zfeuers1/z-zener-zero/components/MAX-M10S-00B/MAX-M10S-00B.md

# MAX-M10S

## Standard precision GNSS module

### Professional grade

#### Integration manual



#### Abstract

This document describes the features and application of the u-blox MAX-M10S module. The MAX-M10S module provides an ultra-low-power standard precision GNSS receiver for high-performance asset-tracking applications.# Document information

|  Title | MAX-M10S  |
| --- | --- |
|  Subtitle | Standard precision GNSS module  |
|  Document type | Integration manual  |
|  Document number | UBX-20053088  |
|  Revision and date | R04  |
|  Disclosure restriction | C1-Public  |

This document applies to the following products:

|  Product name | Type number | FW version | IN/PCN reference | RN reference  |
| --- | --- | --- | --- | --- |
|  MAX-M10S | MAX-M10S-00B-01 | ROM SPG 5.10 | UBX-22012689 | UBX-22001426  |

u-blox or third parties may hold intellectual property rights in the products, names, logos and designs included in this document. Copying, reproduction, or modification of this document or any part thereof is only permitted with the express written permission of u-blox. Disclosure to third parties is permitted for clearly public documents only. The information contained herein is provided "as is" and u-blox assumes no liability for its use. No warranty, either express or implied, is given, including but not limited to, with respect to the accuracy, correctness, reliability and fitness for a particular purpose of the information. This document may be revised by u-blox at any time without notice. For the most recent documents, visit www.u-blox.com. Copyright © 2023, u-blox AG.# Contents 

1 System description ..... 6
1.1 Overview ..... 6
1.2 Architecture ..... 6
1.2.1 Block diagram ..... 6
1.3 Pin assignment ..... 7
2 Receiver configuration ..... 9
2.1 Basic receiver configuration ..... 9
2.1.1 Basic hardware configuration ..... 9
2.1.2 Internal LNA mode configuration ..... 9
2.1.3 GNSS signal configuration ..... 10
2.1.4 Communication interface configuration ..... 11
2.1.5 Message output configuration ..... 11
2.1.6 Antenna supervisor configuration ..... 12
2.1.7 High performance navigation update rate configuration ..... 13
2.2 Navigation configuration ..... 14
2.2.1 Dynamic platform ..... 14
2.2.2 Navigation input filters ..... 15
2.2.3 Navigation output filters ..... 16
2.2.4 Odometer filters ..... 16
2.2.5 Static hold ..... 17
2.2.6 Freezing the course over ground ..... 18
2.2.7 Super-Signal (Super-S) technology ..... 19
2.3 OTP memory configuration ..... 19
3 Receiver functionality ..... 20
3.1 Augmentation systems ..... 20
3.1.1 SBAS ..... 20
3.1.2 QZSS SLAS ..... 21
3.2 Communication interfaces and PIOs ..... 22
3.2.1 UART ..... 22
3.2.2 I2C ..... 23
3.2.3 PIOs ..... 26
3.3 Antenna ..... 28
3.3.1 Antenna supervisor ..... 28
3.4 Forcing receiver reset ..... 34
3.5 Security ..... 35
3.5.1 Configuration locking ..... 35
3.6 Power management ..... 35
3.6.1 Continuous mode ..... 35
3.6.2 Power save mode ..... 36
3.6.3 Backup modes ..... 42
3.7 Time ..... 42
3.7.1 Receiver local time ..... 43
3.7.2 GNSS time bases ..... 433.7.3 Navigation epochs ..... 44
3.7.4 iTow timestamps ..... 45
3.7.5 Time validity ..... 45
3.7.6 UTC representation ..... 46
3.7.7 Leap seconds ..... 46
3.7.8 Date ambiguity ..... 47
3.8 Time mark ..... 47
3.9 Time pulse ..... 48
3.9.1 Recommendations ..... 49
3.9.2 Time pulse configuration ..... 50
3.10 Time maintenance ..... 51
3.10.1 Real-time clock ..... 51
3.10.2 Time assistance ..... 51
3.10.3 Frequency assistance ..... 52
3.10.4 Clock drift assistance ..... 52
3.11 Protection level ..... 52
3.11.1 Introduction ..... 52
3.11.2 Interface ..... 53
3.11.3 Expected behavior ..... 54
3.12 Multiple GNSS assistance (MGA) ..... 54
3.12.1 Authorization ..... 55
3.12.2 Preserving MGA and operational data during power-off ..... 55
3.12.3 AssistNow offline ..... 55
3.12.4 AssistNow autonomous ..... 58
3.13 Data batching ..... 61
3.13.1 Introduction ..... 61
3.13.2 Setting up the data batching ..... 61
3.13.3 Retrieval ..... 62
3.14 CloudLocate ..... 62
3.14.1 CloudLocate measurements ..... 63
4 Hardware integration ..... 64
4.1 Power supply ..... 64
4.1.1 VCC ..... 64
4.1.2 V_IO ..... 64
4.1.3 V_BCKP ..... 64
4.1.4 Supply design examples ..... 65
4.2 RF interference ..... 66
4.2.1 In-band interference ..... 66
4.2.2 Out-of-band interference ..... 66
4.2.3 Spectrum analyzer ..... 67
4.3 RF front-end ..... 68
4.3.1 Internal LNA modes ..... 68
4.3.2 Out-of-band blocking immunity ..... 69
4.3.3 Out-of-band rejection ..... 70
4.3.4 Antenna power supply ..... 70
4.4 Layout ..... 71
4.4.1 Package footprint, copper and solder mask ..... 72
5 Product handling ..... 755.1 Safety ..... 75
5.1.1 ESD precautions ..... 75
5.1.2 Safety precautions ..... 75
5.2 Packaging ..... 76
5.2.1 Reels ..... 76
5.2.2 Tapes ..... 76
5.2.3 Moisture sensitivity level ..... 77
5.3 Soldering ..... 77
Appendix ..... 81
A Migration ..... 81
A. 1 Hardware changes ..... 81
A. 2 Software changes ..... 83
B Reference designs ..... 85
B. 1 Typical design ..... 85
B. 2 Antenna supervisor designs ..... 86
C External components ..... 89
C. 1 Standard capacitors ..... 89
C. 2 Standard resistors ..... 89
C. 3 Inductors ..... 89
C. 4 Operational amplifier ..... 90
C. 5 Open drain buffers ..... 90
C. 6 Antenna supervisor switch transistors ..... 90
Related documents ..... 91
Revision history ..... 92# 1 System description 

This section gives an overview of the MAX-M10S receiver, and outlines the basics of operation with the receiver.

### 1.1 Overview

MAX-M10S module features the u-blox M10 standard precision GNSS platform and provides exceptional sensitivity and acquisition time for all L1 GNSS signals.

The M10 platform supports concurrent reception of four GNSS (GPS, GLONASS, Galileo, and BeiDou). The high number of visible satellites enables the receiver to select the best signals. This maximizes the position availability, in particular under challenging conditions such as in deep urban canyons.
u-blox Super-S (Super-Signal) technology offers great RF sensitivity and can improve the dynamic position accuracy with small antennas or in non-line-of-sight scenarios.

The extremely low power consumption of 25 mW in continuous tracking mode allows great power autonomy for all battery-operated devices, such as asset trackers, without compromising on GNSS performance.

For maximum sensitivity in passive antenna designs, MAX-M10S integrates an LNA followed by a SAW filter in the RF path.

MAX-M10S offers backwards pin-to-pin compatibility with products from the previous u-blox generations, which saves the designer's effort and reduces costs when upgrading designs to the advanced low-power u-blox M10 GNSS technology.

### 1.2 Architecture

The MAX-M10S receiver provides all the necessary RF and baseband processing to enable multiconstellation operation. The block diagram below shows the key functionality.

### 1.2.1 Block diagram



Figure 1: MAX-M10S block diagram# 1.3 Pin assignment 



Figure 2: MAX-M10S pin assignment

| Pin no. | Name | PIO no. | I/O | Description | Remarks |
| :--: | :--: | :--: | :--: | :--: | :--: |
| 1 | GND | - | - | - | Connect to GND |
| 2 | TXD | 1 | 0 | UART TX | If not used, leave open. Alternative functions ${ }^{1}$. |
| 3 | RXD | 0 | I | UART RX | If not used, leave open. Alternative functions ${ }^{1}$. |
| 4 | TIMEPULSE | 4 | 0 | Time pulse signal | See section TIMEPULSE for more information. Alternative functions ${ }^{1}$. |
| 5 | EXTINT | 5 | I | External interrupt | See EXTINT for more information. Alternative functions ${ }^{1}$. |
| 6 | V_BCKP | - | I | Backup voltage supply. | Leave open if no external backup supply. See V_BCKP for more information. |
| 7 | V_IO | - | I | IO voltage supply | See V_IO for more information. |
| 8 | VCC | - | I | Main voltage supply | See VCC for more information. |
| 9 | RESET_N | - | I | System reset (active low) | It has to be low for at least 1 ms to trigger a reset. Leave open if not used. <br> See RESET_N section for more information. |
| 10 | GND | - | - | - | Connect to GND |
| 11 | RF_IN | - | I | GNSS signal input | The RF signal line is DC blocked internally. The line must match the $50 \Omega$ impedance. <br> See sections RF front-end and Layout for more information about the RF signal considerations. |
| 12 | GND | - | - | - | Connect to GND |
| 13 | LNA_EN | - | 0 | On/Off external LNA or active antenna | This pin cannot be used for another purpose as it also controls the internal LNA. <br> See LNA_EN for more information. |

[^0]
[^0]:    1 Alternatively, this pin can be used for ANT_DETECT, ANT_SHORT_N, TX_READY, and Data batching. Care must be taken when the assigned function sets the pin as an output.| Pin no. | Name | PIO no. | I/O | Description | Remarks |
| :--: | :--: | :--: | :--: | :--: | :--: |
| 14 | VCC_RF | - | 0 | Output voltage RF section | This pin supplies a filtered voltage that can be used for optional external active antenna or LNA. This pin is internally connected to VCC through a ferrite bead. |
| 15 | VIO_SEL | - | I | Voltage selector for V_IO supply | Connect to GND for 1.8 V supply, or leave open for 3.3 V supply |
| 16 | SDA | 2 | I/O | I2C data | If not used, leave open. Alternative functions ${ }^{1}$. |
| 17 | SCL | 3 | I | I2C clock | If not used, leave open. Alternative functions ${ }^{1}$. |
| 18 | SAFEBOOT_N | - | I | Safeboot mode | To enter safeboot mode, set this pin to low at receiver's startup. Otherwise, leave it open. <br> The SAFEBOOT_N pin is internally connected to TIMEPULSE pin through a $1 \mathrm{k} \Omega$ series resistor. |

Table 1: MAX-M10S pin assignment# 2 Receiver configuration 

The configuration determines all aspects of the GNSS receiver operation and therefore this section is essential reading for the successful integration of the MAX-M10S.

MAX-M10S is configured using UBX configuration interface keys. The configuration database in the receiver's RAM holds the current configuration, which is used by the receiver at runtime. It is constructed on startup of the receiver from several sources of configuration. For more information on receiver configuration, see the interface description [3].

A configuration setting stored in the RAM remains effective until power-down or reset. The RAM content is cleared by any of the following:

- Activating the RESET_N pin
- A UBX-CFG-RST message excluding GNSS stop (resetMode 0x08) and GNSS start (resetMode $0 \times 09)$
- Entering software standby mode
- Using external control in power save mode (PSM) to enter the inactive state
- Entering the off state of the PSM on/off operation (PSMOO)

It is therefore recommended to apply runtime configuration on both RAM and battery-backed RAM (BBR) layers.

The configuration stored in BBR is also cleared by a RESET_N signal or a UBX-CFG-RST message with reset mode set to a hardware reset (resetMode $0 \times 00$ and $0 \times 04$ ), but otherwise will be used as long as the backup battery supply remains.

CAUTION The configuration interface has changed from earlier u-blox positioning receivers. Users must adopt the configuration interface described in this document.

The configuration interface settings are stored in a database consisting of separate configuration items. An item is made up of a pair consisting of a key ID and a value. Related items are grouped together and identified under a common group name: CFG-GROUP-*; a convention used in u-center 2 and within this document. Within u-center 2, a configuration group is identified as "Group name" and the configuration item is identified as the "item name" in the "Device configuration" window.

The UBX messages available to change or poll the configurations are the UBX-CFG-VALSET, UBX-CFG-VALGET, and UBX-CFG-VALDEL messages. For more information about these messages and the configuration keys, see the configuration interface section in the interface description [3].

### 2.1 Basic receiver configuration

This section summarizes the basic receiver configuration most commonly used.

### 2.1.1 Basic hardware configuration

The MAX-M10S receiver is configured with the default settings during the module production. The receiver starts up and is fully operational as soon as proper power supply, communication interfaces and antenna signal from the host application device are connected.

### 2.1.2 Internal LNA mode configuration

u-blox 10 receivers support three modes for the internal low-noise amplifier (LNA): normal gain, low gain, and bypass mode. The MAX-M10S default is the low-gain mode. With a high-gain external active antenna, the bypass mode can be used. The normal-gain mode is not recommended for MAXM10S.The internal LNA mode can be configured at run time in BBR and RAM memory using the configuration item CFG-HW-RF_LNA_MODE and applying a software reset by sending UBX-CFGRST message. Refer to Forcing receiver reset for more information.

The internal LNA mode can also be permanently configured in the receiver's one-time programmable (OTP) memory. Changes to the bits in the OTP memory cannot be modified after they are programmed. The OTP configuration is only done once in production, and is subsequently applied automatically at every startup.

The default gain mode is pre-configured in the receiver and does not require configuration in production. The configuration string for setting the internal LNA mode in the OTP memory is given in Table 2.

OTP configuration is permanent and cannot be reverted. Configuration at run time in BBR and RAM memory is still possible.

| Internal LNA mode | Configuration string |
| :-- | :-- |
| Low gain | Default |
| Bypass | B5 62 06 41 10 00 03 00 05 1F 79 B2 0A E5 28 EF 12 05 9F FF FF FF 62 FB |

Table 2: Internal LNA mode configuration in OTP memory
To configure the internal LNA mode in OTP memory:

1. Power up the system.
2. Test the communication interface by polling the UBX-MON-VER message.
3. Send the configuration string in Table 2.
4. Power the receiver off and on or send UBX-CFG-RST message (the reset type must be set to a hardware reset). The new internal LNA setting is applied at startup.
5. Verify that the configuration item is correctly set by polling CFG-HW-RF_LNA_MODE at RAM layer using the UBX-CFG-VALGET message.
6. The OTP memory configuration is completed.

# 2.1.3 GNSS signal configuration 

MAX-M10S supports concurrent reception of four major GNSS constellations using the GPS L1C/A, Galileo E1, BeiDou B1C, and GLONASS L1OF signals. BeiDou B1I signal is also supported, but cannot be used simultaneously with BeiDou B1C or GLONASS L1OF signals. The default configuration is concurrent reception of GPS, Galileo and BeiDou B1I with QZSS and SBAS enabled.

BeiDou B1I signal cannot be used simultaneously with BeiDou B1C or GLONASS L1OF signals.
GNSS constellations and signals can be configured using the CFG-SIGNAL-* configuration group. Each GNSS constellation can be enabled or disabled independently except for QZSS and SBAS, which are functional only with GPS. In addition to the configuration key for each constellation, there is a configuration key for each signal supported by the firmware. Unsupported combinations are rejected with a UBX-ACK-NAK message, and the warning "inv sig cfg" is sent via UBX-INF and NMEATXT messages (if enabled).

For example, if CFG-SIGNAL-GPS_ENA is set to zero, all signals from the GPS constellation are disabled. Alternatively, if CFG-SIGNAL-GPS_L1CA_ENA is set to zero, only the GPS L1 C/A signal is disabled.

Any change to the signal configuration items triggers a restart of the GNSS subsystem. This takes a short time period, so the host application should wait for message acknowledgement and a margin of 0.5 seconds prior to sending any further commands.It is recommended to enable QZSS L1C/A when GPS L1C/A is enabled in order to mitigate possible cross-correlation issues between the signals.

Refer to the Interface description [3] for more information on the CFG-SIGNAL-* configuration group.

# 2.1.3.1 BeiDou B1I and B1C signals

BeiDou B1I and B1C signals differ in terms of the center frequency, bandwidth, and modulation. Therefore, there are differences in performance and supported GNSS signals and features.

## Benefits of using BeiDou B1I signal:

BeiDou B1I offers superior GNSS performance. High start-up sensitivity and fast time-to-first-fix (TTFF) enable acquisition of a large number of BeiDou satellites. The tracking and reacquisition sensitivity for acquired signals is approximately at the same level for BeiDou B1I and B1C.

- Faster TTFF and higher start-up sensitivity. BeiDou B1I signals are acquired significantly faster and at a lower signal level than BeiDou B1C signals.
- Better availability. Higher start-up sensitivity results in a larger number of BeiDou satellites tracked and used in navigation solution especially at low signal level.
- AssistNow Online support. Enhanced start-up sensitivity and TTFF.
- Power save mode (PSM) support. PSM cyclic tracking (PSMCT) and on/off (PSMOO) mode operation are supported.

## Benefits of using BeiDou B1C signal:

BeiDou B1C signal has the same center frequency as GPS L1 C/A enabling concurrent use of 4 GNSS constellations. Multi-GNSS configurations with BeiDou B1C also have a lower power consumption compared to those with BeiDou B1I.

- Concurrent reception of 4 GNSS with GPS L1 C/A, Galileo E1, BeiDou B1C, and GLONASS L1OF.
- Lower power consumption. No additional frequency band required for BeiDou B1C in multiGNSS constellations resulting in a lower power consumption during acquisition and tracking phases.

### 2.1.4 Communication interface configuration

Several configuration groups allow configuring the operation mode of the communication interfaces. These include parameters for the data framing, transfer rate and enabled input/output protocols. See Communication interfaces and PIOs section for details. The configuration groups available for each interface are:

|  Interface | Configuration groups  |
| --- | --- |
|  UART | CFG-UART1-*, CFG-UART1INPROT-*, CFG-UART1OUTPROT-*  |
|  I2C | CFG-I2C-*, CFG-I2CINPROT-*, CFG-I2COUTPROT-*, CFG-TXREADY-*  |

Table 3: Interface configuration The UART baudrate in MAX-M10S is configured to 9600 baud which is different to the firmware default. This ensures backwards compatibility with previous generations of u-blox MAX modules.

### 2.1.5 Message output configuration

The receiver supports two protocols for output messages: industry-standard NMEA and u-blox UBX. Any message type can be enabled or disabled individually and the output rate is configurable.The message output rate is related to the frequency of an event. For example, the output message UBX-NAV-PVT (position, velocity, and time solution) is related to the navigation event, which generates a navigation epoch. In this case, the rate for each navigation epoch is defined by the configuration keys CFG-RATE-MEAS and CFG-RATE-NAV. For example, a value of 1000 ms in CFG-RATE-MEAS indicates that a measurement is done every second. If CFG-RATE-NAV is set to one (1), the solution is calculated for every measurement. This means that a navigation epoch is calculated every 1000 ms . If the rate is set to two (2), only the second measurement is used and the navigation epoch is calculated every two seconds. The same result is obtained if CFG-RATE-MEAS is set to 2000 ms , and CFG-RATE-NAV is set to one (1). Every 2000 ms a measurement is done, and in every measurement, a navigation epoch is calculated. However, this second option demands fewer resources and is the correct procedure when the navigation rate is changed. Setting a navigation rate value higher than one (1) is only needed when it is required that the raw measurement data is output at a higher rate than the navigation data.

The output rate for each message is defined in the CFG-MSGOUT-* configuration group. If the output rate of the message is set to one (1) on the UART interface, CFG-MSGOUT-UBX_NAV_PVT_UART1 = 1, the message is output for every navigation epoch. If the rate is set to two (2), the message is output for every other navigation epoch. If the rate is zero (0), then corresponding message is not output. As seen in this example, the rates of the output messages are individually configurable per communication interface.

Some messages, such as UBX-MON-VER, are non-periodic and are only output as an answer to a poll request.

The UBX-INF-* and NMEA-Standard-TXT information messages are non-periodic output messages that do not have a message rate configuration. Instead they can be enabled for each communication interface via the CFG-INFMSG-* configuration group.

All message output is additionally subject to the protocol configuration of the communication interfaces. Messages of a given protocol are not output unless the protocol is enabled for output on the interface. See Communication interface configuration for details.

The output rate of the NMEA-GxGSV message on the UART interface is configured to 5 in MAXM10S, which is different to the firmware default in order to avoid overloading the communication interface and buffers.

# 2.1.6 Antenna supervisor configuration 

This section gives an overview of the antenna supervisor configuration keys. The implementation of the antenna supervisor and a detailed description can be found in Antenna supervisor.

The antenna supervisor is used to control an active antenna. The configuration of the antenna supervisor allows the following:

- Control voltage supply to the antenna, which allows the antenna supervisor to cut power to the antenna in the event of a short circuit or optimize power to the antenna in power save modes.
- Detect a short circuit in the antenna and automatically recover the antenna supply after the short circuit is no longer present.
- Detect an open circuit, which can be used to indicate if the antenna has been disconnected.

Using some antenna supervisor features may require disabling the UART or I2C interface and reconfiguring the PIOs as antenna supervisor pins.

Table 4 describes the configuration items.

| Configuration item | Description | Comments |
| :-- | :-- | :-- |
| CFG-HW-ANT_CFG_VOLTCTRL | Enable active antenna voltage control |  || Configuration item | Description | Comments |
| :--: | :--: | :--: |
| CFG-HW-ANT_CFG_SHORTDET | Enable short circuit detection |  |
| CFG-HW-ANT_CFG_SHORTDET_POL | Short antenna detection polarity | Set to 1 if the required logic polarity is active-low (default). |
| CFG-HW-ANT_CFG_OPENDET | Enable open circuit detection |  |
| CFG-HW-ANT_CFG_OPENDET_POL | Open antenna detection polarity | Set to 1 if the required logic polarity is active-low (default). |
| CFG-HW-ANT_CFG_PWRDOWN | Power down antenna supply if short circuit is detected | Requires CFG-HW- <br> ANT_CFG_VOLTCTRL and CFG-HW- <br> ANT_CFG_SHORTDET to be enabled. |
| CFG-HW-ANT_CFG_PWRDOWN_POL | Power down antenna logic polarity | Set to 1 if the required logic polarity is active-high (default). |
| CFG-HW-ANT_CFG_RECOVER | Enable auto-recovery in the event of a short circuit | To use this feature, enable short circuit detection and CFG-HW- <br> ANT_CFG_PWRDOWN. |
| CFG-HW-ANT_SUP_SWITCH_PIN | PIO number of the pin used for switching antenna supply | PIO5 is recommended if available. This pin can be used as an LNA_EN signal to control an external LNA, especially if software standby mode or power save mode on/off (PSMOO) operation is used. |
| CFG-HW-ANT_SUP_SHORT_PIN | PIO number of the pin used for detecting a short circuit in the antenna supply | UART or I2C pins can be used for the short detection, depending on which interface is used for communication. |
| CFG-HW-ANT_SUP_OPEN_PIN | PIO number of the pin used for detecting open/disconnected antenna | UART or I2C pins can be used for the short detection, depending on which interface is used for communication. |

Table 4: Antenna supervisor configuration
It is possible to obtain the status of the antenna supervisor from the UBX-MON-RF message. Refer to the interface manual for the description of the antStatus and antPower fields [3]. In addition, any changes in the status of the antenna supervisor are reported to the host interface as ANTSTATUS in NMEA notice messages.

| ANTSTATUS | Description |
| :-- | :-- |
| OFF | Antenna is off |
| ON | Antenna is on |
| DONTKNOW | Antenna power status is not known |

Table 5: Antenna power status

# 2.1.7 High performance navigation update rate configuration 

The navigation update rate is a GNSS configuration item which determines how many position fixes the receiver calculates and outputs per second. The maximum achievable navigation update rate depends on the number of GNSS signals the receiver is tracking. Depending on the geographical location and GNSS constellations enabled, the number of tracking channels in use may vary. In particular, in Asia there is a large number of BeiDou satellites available potentially limiting the maximum achievable navigation update rate. In regions with a lower number of available BeiDou satellites, a higher navigation rate is achieved.

The maximum navigation update rate given in the datasheet is provided for a minimum of $98 \%$ position fix rate, i.e., up to $2 \%$ position fixes can get lost in case of high availability of signals. The navigation update rate can be increased beyond the maximum value stated in the datasheet. However, this may result in a reduced fix rate if a very large number of satellites is tracked.u-blox M10 devices are optimized for low power consumption and come with the default CPU clock rate that supports the default navigation update rate stated in the product datasheet. However, it is possible to achieve a higher navigation update rate by configuring the device for a higher clock rate. This supports the high performance navigation update rate with minor increase in power consumption.

For the high navigation update rates, increase the communication speed and reduce the number of enabled messages.

The high performance navigation update rate can be configured in the device's one-time programmable (OTP) memory. The OTP configuration is only done once, and is subsequently applied automatically at every startup. The configuration string for setting the high CPU clock rate in the OTP memory is given in Table 6. This occupies 18 bytes of OTP memory space.

Changes made in the OTP configuration are permanent and cannot be reverted.

|  CPU clock | Configuration string  |
| --- | --- |
|  Default CPU clock | Default  |
|  High CPU clock | B5 62064110000300041 F 545 E 79 BF 28 EF 1205 FD FF FF FF 8F 0D B5 6206411 C 000401 A4 10 BD 34 F9 1228 EF 12050500 A4 4000 B0 710 B 0 A 00 A4 4000 D8 B8 05 DE AE  |

Table 6: High performance navigation update rate configuration in OTP memory To configure the high performance navigation update rate in OTP memory:

1. Power up the device.
2. Test the communication interface by polling the UBX-MON-VER message.
3. Send the configuration string provided in Table 6. The device returns two UBX-ACK-ACK messages with sequence of bytes B5 620501020006414 F 78.
4. Set the device reset to a hardware reset. Power the device off and on or send the UBX-CFG-RST message to the device. The higher clock setting is applied at startup.
5. To verify that the configuration item is correctly set,
6. send the following sequence to the receiver: B5 62068 B 1400000400000100 A4 4003 00 A4 400500 A4 400 A 00 A4 404 C 15
7. receive a UBX-CFG-VALGET message with the following sequence: B5 62068 B 24000104 00000100 A4 4000 B0 710 B 0300 A4 4000 B0 710 B 0500 A4 4000 B0 710 B 0 A 00 A4 4000 D8 B8 057681
8. receive a UBX-ACK-ACK message with the following sequence: B5 6205010200068 B 99 C2
9. The OTP memory configuration is completed and verified.

# 2.2 Navigation configuration

This section presents various configuration options related to the navigation engine. These options can be configured through CFG-NAVSPG-* configuration keys.

### 2.2.1 Dynamic platform

The dynamic platform model can be configured through the CFG-NAVSPG-DYNMODEL configuration item. For the supported dynamic platform models and their details, see Table 7 and Table 8.

|  Platform | Description  |
| --- | --- |
|  Portable | Applications with low acceleration, e.g. portable devices. Suitable for most situations.  ||  Platform | Description  |
| --- | --- |
|  Stationary | Used in timing applications (antenna must be stationary) or other stationary applications. Velocity restricted to $0 \mathrm{~m} / \mathrm{s}$. Zero dynamics assumed.  |
|  Pedestrian | Applications with low acceleration and speed, e.g. how a pedestrian would move. Low acceleration assumed.  |
|  Automotive | Used for applications with equivalent dynamics to those of a passenger car. Low vertical acceleration assumed.  |
|  At sea | Recommended for applications at sea, with zero vertical velocity. Zero vertical velocity assumed. Sea level assumed.  |
|  Airborne <1g | Used for applications with a higher dynamic range and greater vertical acceleration than a passenger car. No 2D position fixes supported.  |
|  Airborne <2g | Recommended for typical airborne environments. No 2D position fixes supported.  |
|  Airborne <4g | Only recommended for extremely dynamic environments. No 2D position fixes supported.  |
|  Wrist | Only recommended for wrist-worn applications. Receiver will filter out arm motion.  |

Table 7: Dynamic platform models

|  Platform | Max altitude [m] | Max horizontal velocity [m/s] | Max vertical velocity [m/s] | Sanity check type | Max position deviation  |
| --- | --- | --- | --- | --- | --- |
|  Portable | 12000 | 310 | 50 | Altitude and velocity | Medium  |
|  Stationary | 9000 | 10 | 6 | Altitude and velocity | Small  |
|  Pedestrian | 9000 | 30 | 20 | Altitude and velocity | Small  |
|  Automotive | 6000 | 100 | 15 | Altitude and velocity | Medium  |
|  At sea | 500 | 25 | 5 | Altitude and velocity | Medium  |
|  Airborne <1g | 80000 | 100 | 6400 | Altitude | Large  |
|  Airborne <2g | 80000 | 250 | 10000 | Altitude | Large  |
|  Airborne <4g | 80000 | 500 | 20000 | Altitude | Large  |
|  Wrist | 9000 | 30 | 20 | Altitude and velocity | Medium  |

Table 8: Dynamic platform model details Applying dynamic platform models designed for high acceleration systems (e.g. airborne <2g) can result in a higher standard deviation in the reported position.

If a sanity check against a limit of the dynamic platform model fails, then the position solution becomes invalid. Table 8 shows the types of sanity checks which are applied for a particular dynamic platform model.

# 2.2.2 Navigation input filters

The navigation input filters in the CFG-NAVSPG-* configuration group control how the navigation engine handles the input data that comes from the satellite signal.

|  Configuration item | Description  |
| --- | --- |
|  CFG-NAVSPG-FIXMODE | By default, the receiver calculates a 3D position fix if possible but reverts to 2D position if necessary (auto 2D/3D). The receiver can be forced to only calculate 2D (2D only) or 3D (3D only) positions.  |
|  CFG-NAVSPG-CONSTR_ALT, CFG-
NAVSPG-CONSTR_ALTVAR | The fixed altitude is used if fixMode is set to 2D only. A variance greater than zero must also be supplied.  |
|  CFG-NAVSPG-INFIL_MINELEV | Minimum elevation of a satellite above the horizon to be used in the navigation solution. Low-elevation satellites may provide degraded accuracy, due to the long signal path through the atmosphere.  |
|  CFG-NAVSPG-INFIL_MINSVS, CFG-
NAVSPG-INFIL_MAXSVS | Minimum and maximum number of satellites to use in the navigation solution. There is an absolute maximum limit of 32 satellites that can be used for navigation.  || Configuration item | Description |
| :-- | :-- |
| CFG-NAVSPG-INFIL_NCNOTHRS, | A navigation solution will only be attempted if there is at least the given number of |
| CFG-NAVSPG-INFIL_CNOTHRS | satellites with signals at least as strong as the given threshold. |

Table 9: Navigation input filter parameters
If the receiver has only three satellites for calculating a position, the navigation algorithm uses a constant altitude to compensate for the missing fourth satellite. This is called a 2D fix. The constant altitude value is taken from the last successful 3D fix using a minimum of four available satellites.
$\square$ u-blox receivers do not calculate any navigation solution with fewer than three satellites.

# 2.2.3 Navigation output filters 

The result of a navigation solution is initially classified by the fix type (as detailed in the fixType field of UBX-NAV-PVT message). This distinguishes between failures to obtain a fix at all ("No Fix") and cases where a fix has been achieved, which are further subdivided into specific types of fixes (for example, 2D, 3D ).

Where a fix has been achieved, the fix is checked to determine whether it is valid or not. A fix is only valid if it passes the navigation output filters as defined in CFG-NAVSPG-OUTFIL. In particular, both PDOP and accuracy values must be below the respective limits.

Important: Users are recommended to check the gnssFixOK flag in the UBX-NAV-PVT or the NMEA valid flag. Fixes not marked as valid should not be used.

UBX-NAV-STATUS message also reports whether a fix is valid in the gpsFixOK flag. These messages have only been retained for backwards compatibility and it is recommended to use the UBX-NAV-PVT message.

### 2.2.4 Odometer filters

### 2.2.4.1 Speed (3D) low-pass filter

The CFG-ODO-OUTLPVEL configuration item activates a speed (3D) low-pass filter. The output of the speed low-pass filter is available in the UBX-NAV-VELNED message (speed field). The filtering level can be set via the CFG-ODO-VELLPGAIN configuration item and must be between 0 (heavy lowpass filtering) and 255 (weak low-pass filtering).

The internal filter gain is computed as a function of speed. Therefore, the level as defined in the CFG-ODO-VELLPGAIN configuration item defines the nominal filtering level for speeds below 5 $\mathrm{m} / \mathrm{s}$.

### 2.2.4.2 Course over ground low-pass filter

The CFG-ODO-OUTLPCOG configuration item activates a course over ground low-pass filter when the speed is below $8 \mathrm{~m} / \mathrm{s}$. The output of the course over ground (also named heading of motion 2D) low-pass filter is available in the UBX-NAV-PVT message (headMot field), UBX-NAV-VELNED message (heading field), NMEA-RMC message (cog field), and NMEA-VTG message (cogt field). The filtering level can be set via the CFG-ODO-COGLPGAIN configuration item and must be between 0 (heavy low-pass filtering) and 255 (weak low-pass filtering).

The filtering level as defined in the CFG-ODO-COGLPGAIN configuration item defines the filter gain for speeds below $8 \mathrm{~m} / \mathrm{s}$. If the speed is $8 \mathrm{~m} / \mathrm{s}$ or higher, no course over ground low-pass filtering is performed.# 2.2.4.3 Low-speed course over ground filter 

The CFG-ODO-USE_COG configuration item activates this feature and the CFG-ODOCOGMAXSPEED, CFG-ODO-COGMAXPOSACC configuration items are used to configure a lowspeed course over ground filter (also named heading of motion 2D). This filter derives the course over ground from position at very low speed. The output of the low-speed course over ground filter is available in the UBX-NAV-PVT message (headMot field), UBX-NAV-VELNED message (heading field), NMEA-RMC message (cog field) and NMEA-VTG message (cogt field). If the low-speed course over ground filter is not configured, then the course over ground is computed as described in section Freezing the course over ground.

### 2.2.5 Static hold

Static hold mode allows the navigation algorithms to decrease the noise in the position output when the velocity is below a predefined "Static Hold Threshold" level. This reduces the position wander caused by environmental factors such as multi-path and improves position accuracy especially in stationary applications. By default, static hold mode is disabled.

The CFG-MOT-GNSSSPEED_THRS configuration item defines the static hold speed threshold. If the speed drops below the defined "Static Hold Threshold", static hold mode is activated. Once static hold mode is active, the position output is kept static and the velocity is set to zero until there is evidence of movement again. Such evidence can be velocity, acceleration, changes of the valid flag (for example, position accuracy estimate exceeding the position accuracy mask, see also section Navigation output filters ), position displacement, etc.

The CFG-MOT-GNSSDIST_THRS configuration item defines the static hold distance threshold. If the distance between the estimated position and the static hold position exceeds the defined threshold, static hold mode is suspended or deactivated until there is evidence of no movement.


Figure 3: Position output in static hold mode

Figure 4: Flowchart of static hold mode

# 2.2.6 Freezing the course over ground 

If the low-speed course over ground filter is deactivated or inactive (see section Low-speed course over ground filter), the receiver derives the course over ground from the GNSS velocity information. If the velocity cannot be calculated with sufficient accuracy (for example, with bad signals) or if the absolute speed value is very low (under $0.1 \mathrm{~m} / \mathrm{s}$ ) then the course over ground value becomes inaccurate too. In this case the course over ground value is frozen, that is, the previous value is kept and its accuracy degrades over time. These frozen values will not be output in the NMEA messages NMEA-RMC and NMEA-VTG unless the NMEA protocol is explicitly configured to do so (see NMEA protocol configuration in the applicable interface description [3]).

Figure 5: Flowchart of course over ground freezing

# 2.2.7 Super-Signal (Super-S) technology 

In normal operating conditions, low signal strength (that is, signal attenuation) indicates possible degradation due to multi-path. The receiver trusts such signals less in order to preserve the quality of the position solution in poor signal environments. This feature can result in degraded performance in situations where the signals are attenuated for another reason, for example due to antenna placement. In this case, the weak signal compensation feature can be used to restore normal performance. There are three possible modes:

- Disabled: no weak signal compensation is performed
- Automatic: the receiver automatically estimates and compensates for the weak signal
- Configured: the receiver compensates for the weak signal based on a configured value

These modes can be selected using CFG-NAVSPG-SIGATTCOMP. In the case of the "configured" mode, the user should input the maximum C/NO observed in a clear-sky environment, excluding any outliers or unusually high values. Choose the configured value carefully, as it can have a large impact on the receiver performance.

### 2.3 OTP memory configuration

MAX-M10S contains a one-time programmable (OTP) memory. This is a non-volatile memory for storing configuration settings and ROM patches permanently in the device. The stored data cannot be modified after it has been initially programmed. The device applies the settings and ROM patches on the device startup.

As the space in the OTP memory is limited, only essential system configuration settings should be stored. The total space used for device configuration and ROM patches in the OTP memory must not exceed 64 bytes. Other settings can be stored in the BBR or sent from the host to the device on each device startup.

Ensure that the final configuration stored and optional ROM patches do not require more than 64 bytes of OTP memory space.# 3 Receiver functionality

This section provides a description of the receiver's functionality.

### 3.1 Augmentation systems

### 3.1.1 SBAS

MAX-M10S is capable of receiving multiple SBAS signals concurrently, even from different SBAS systems (WAAS, EGNOS, etc.). SBAS signals are recommended to be used only for correction data. SBAS signals can also be used for navigation, however they have low weighting and therefore only a minor impact on the navigation solution.

For receiving correction data, MAX-M10S automatically chooses the best SBAS satellite as its primary source. It will select only one since the information received from other SBAS satellites is redundant and could be inconsistent. The selection strategy is determined by the proximity of the satellites, the services offered by the satellite, the configuration of the receiver (test mode allowed/ disallowed, integrity enabled/disabled) and the signal link quality to the satellite.

If corrections are available from the chosen SBAS satellite and used in the navigation calculation, the differential status will be indicated in several output messages such as UBX-NAV-PVT, UBX-NAVSTATUS, UBX-NAV-SAT, NMEA-GGA, NMEA-GLL, NMEA-RMC, and NMEA-GNS. The UBX-NAVSBAS message provides detailed information about which corrections are available and applied. Refer to the interface description [3] for a detailed description of the messages.

The most important SBAS feature for accuracy improvement is the ionosphere correction parameters. The measured data from regional Ranging and Integrity Monitoring Stations (RIMS) are combined to make a Total Electron Content (TEC) map. This map is transferred to the receiver via SBAS satellites to allow a correction of the ionosphere delays on each received signal.

|  Message type | Message content | Source  |
| --- | --- | --- |
|  $0(0 / 2)$ | Test mode | All  |
|  1 | PRN mask assignment | Primary  |
|  $2,3,4,5$ | Fast corrections | Primary  |
|  6 | Integrity | Primary  |
|  7 | Fast correction degradation | Primary  |
|  9 | Satellite navigation (ephemeris) | All  |
|  10 | Degradation | Primary  |
|  12 | Time offset | Primary  |
|  17 | Satellite almanac | All  |
|  18 | Ionosphere grid point assignment | Primary  |
|  24 | Mixed fast / long-term corrections | Primary  |
|  25 | Long-term corrections | Primary  |
|  26 | Ionosphere delays | Primary  |

Table 10: Supported SBAS messages Each satellite serves a specific region and its correction signal is only useful within that region. Planning is crucial to determine the best possible configuration, especially in areas where signals from different SBAS systems can be received:- Example 1 - SBAS receiver in North America: In eastern parts of North America, make sure that EGNOS satellites do not take preference over WAAS satellites. The satellite signals from the EGNOS system should be disallowed by using the PRN scan mask (configuration key CFG-SBAS-PRNSCANMASK).
- Example 2 - SBAS receiver in Europe: Some WAAS satellite signals can be received in western parts as well as GAGAN SBAS satellites in some parts of Europe, therefore it is recommended that the satellites from all but the EGNOS system should be disallowed using the PRN scan mask.

Although u-blox receivers try to select the best available SBAS correction data, it is recommended to configure them to exclude unwanted SBAS satellites.

To configure the SBAS functionality, use the CFG-SBAS-* configuration group.

| Parameter | Description |
| :-- | :-- |
| CFG-SIGNAL-SBAS_ENA | Enabled/disabled status of the SBAS subsystem |
| CFG-SBAS-USE_TESTMODE | Allow/disallow SBAS usage from satellites in test mode |
| CFG-SBAS-USE_RANGING | Use the SBAS satellites for navigation (ranging) |
| CFG-SBAS-USE_DIFFCORR | Combined enable/disable switch for fast, long-term, and ionosphere corrections |
| CFG-SBAS-USE_INTEGRITY | Apply integrity information data |
| CFG-SBAS-PRNSCANMASK | Allows selectively enabling/disabling SBAS satellites |

Table 11: SBAS configuration parameters
When SBAS integrity data is applied, the navigation engine stops using all signals for which no integrity data is available (including all non-GPS signals). It is not recommended to enable SBAS integrity on borders of SBAS service regions in order not to inadvertently restrict the number of available signals.

SBAS integrity information is required for at least five GPS satellites. If this condition is not met, SBAS integrity data will not be applied.

When the receiver switches from a solution using correction data to a standard position solution, the reference frame of the output position will switch from that of the correction data to that of the standard position solution. For an SBAS solution, this reference frame will be aligned within a few cm of WGS84 (and modern ITRF realizations).

# 3.1.2 QZSS SLAS 

QZSS SLAS (Sub-meter Level Augmentation Service) is an augmentation technology, which provides correction data for pseudoranges of GPS, QZSS, and other major GNSS satellites. The correction stream is transmitted on the L1S signal at the L1 frequency ( 1575.42 MHz ).

For more information on QZSS SLAS, visit qzss.go.jp/en/.
Multiple QZSS SLAS signals can be received simultaneously. When receiving QZSS SLAS correction data, MAX-M10S will autonomously select the best QZSS satellite. The selection strategy is determined by the quality of the QZSS L1S signals, the receiver configuration (test mode allowed or not), and the location of the receiver with respect to the QZSS SLAS coverage area. When outside of this coverage area, the receiver will likely fall back to using SBAS corrections.

If QZSS SLAS corrections are used in the navigation solution, the differential status will be indicated in several output messages such as UBX-NAV-PVT, UBX-NAV-STATUS, UBX-NAV-SAT, NMEA-GGA, NMEA-GLL, NMEA-RMC, and NMEA-GNS. The UBX-NAV-SLAS message provides detailed information about which corrections are available and applied. Refer to the interface description [3] for a detailed description of the messages.| Message type | Message content |
| :-- | :-- |
| 0 | Test mode |
| 47 | Monitoring station information |
| 48 | PRN mask |
| 49 | Data issue number |
| 50 | DGPS correction |
| 51 | Satellite health |

Table 12: Supported QZSS L1S SLAS messages for navigation enhancement
Use the configuration key CFG-SIGNAL-QZSS_L1S_ENA to enable QZSS L1S signal. For further QZSS SLAS functionality, use the CFG-QZSS-USE_SLAS* configuration keys.

| Parameter | Description |
| :-- | :-- |
| CFG-QZSS-USE_SLAS_DGNSS | Apply QZSS SLAS corrections |
| CFG-QZSS-USE_SLAS_TESTMODE | Allow the correction provided by QZSS satellites that are in test mode |
| CFG-QZSS- <br> USE_SLAS_RAIM_UNCORR | If this configuration is set, the receiver will try to estimate the position by using only <br> corrected measurements; if all corrected measurements are not available, it will not <br> use any corrections. If this configuration is not set, the receiver will mix corrected <br> and uncorrected measurements for the navigation solution. |

Table 13: QZSS SLAS configuration parameters
If the RAIM option is set, QZSS is the only GNSS time system that measurements can observe.

# 3.2 Communication interfaces and PIOs 

MAX-M10S supports communication over UART and I2C interfaces for communication with a host CPU. Each protocol can be enabled on several interfaces at the same time with individual settings for, for example, baud rate, message rates, and so on. In MAX-M10S, several protocols can be enabled on a single interface at the same time.

### 3.2.1 UART

MAX-M10S supports a Universal Asynchronous Receiver/Transmitter (UART) port consisting of an RX and a TX line. The UART can be used as a host interface which supports a configurable baud rate and protocol selection.

Neither handshaking signals nor hardware flow control signals are supported.
The UART baud rate can be configured for selected speeds. Different rates than these speeds are not supported for transmission and reception.

The UART RX interface will be disabled when more than 100 frame errors are detected during a one-second period. This can happen if the wrong baud rate is used or the UART RX pin is grounded. An error message appears when the UART RX interface is re-enabled at the end of the one-second period.

| Baud rate | Data bits | Parity | Stop bits |
| :-- | :-- | :-- | :-- |
| 4800 | 8 | none | 1 |
| 9600 | 8 | none | 1 |
| 19200 | 8 | none | 1 |
| 38400 | 8 | none | 1 |
| 57600 | 8 | none | 1 |
| 115200 | 8 | none | 1 || Baud rate | Data bits | Parity | Stop bits |
| :-- | :-- | :-- | :-- |
| 230400 | 8 | none | 1 |
| 460800 | 8 | none | 1 |
| 921600 | 8 | none | 1 |

Table 14: Possible UART interface configurations
Allow a short time delay of typically 100 ms between sending a baud rate change message and providing input data at the new rate. Otherwise some input characters may be ignored or the port could be disabled until the interface is able to process the new baud rate.

The default baud rate is 9600 baud. Using a lower baud rate may cause buffering problems.
If there is too much data for the interface's bandwidth, the output buffer will fill up. Once the buffer space is exceeded, new messages to be sent will be dropped. To prevent message loss, the baud rate and the number of enabled messages should be selected carefully.

# 3.2.2 I2C 

An I2C interface is available for communication with an external host CPU in I2C Fast-mode. Backwards compatibility with Standard-mode I2C bus operation is not supported. The interface can be operated only in slave mode with a maximum bit rate of $400 \mathrm{kbit} / \mathrm{s}$. The interface can make use of clock stretching by holding the SCL line LOW to pause a transaction. In this case, the bit transfer rate is reduced. The maximum clock stretching time is 20 ms .

The SCL and SDA pins have internal pull-up resistors which should be sufficient for most applications. However, depending on the clock speed of the host and the capacitive load on the I2C lines, additional external pull-up resistors may be necessary. The higher the speed and the capacitance load, the lower the pull-up resistor needs to be.

To poll or set the I2C address, use the CFG-I2C-ADDRESS configuration item (see the u-blox M10 interface description [3]). The CFG-I2C-ADDRESS configuration item is an 8-bit value containing the I2C address in the 7 most significant bits plus a 0 as the least significant bit. Thus, the default address becomes $0 \times 84(10000100)$.

In designs where the host uses the same I2C bus to communicate with more than one u-blox receiver, each receiver's I2C address must be configured with a different value.

### 3.2.2.1 I2C register layout

As shown in Figure 6, there are 256 registers. The data registers 0 to 252, at addresses $0 \times 00$ to $0 x F C$, contain reserved information and must not be used. Hence, only the last three registers are left for communication. The registers $0 x F D$ and $0 x F E$ contain the currently available number of bytes to be read, while the register $0 x F F$ buffers the message stream. The $0 x F F$ address delivers a $0 x F F$ byte value if there is no data awaiting for transmission, or all the bytes have been read.

Figure 6: I2C register layout

# 3.2.2.2 Read access types 

The host can choose one of the following two modes:

- Random read access: the master first reads the number of available bytes at the 0xFD and 0xFE before accessing the data at 0xFF.
- Current address read access: the master directly reads the data at the register 0xFF, without knowing first if there is any data waiting. If there is no data, the read result is a 0xFF byte value. This mode basically skips the first step of the "random read access", as it does not address to any particular register.

Figure 7 shows the format of the "random access" form of the request.
Following the start condition from the master, the 7-bit device address and the RW bit (which is a logic low for write access) are clocked onto the bus by the master transmitter. The receiver answers with an acknowledge (logic low) to indicate that it recognizes the address.

Next, the 8-bit address of the register to be read must be written to the bus (0xFD for u-blox receivers). Following the receiver's acknowledgment, the master again triggers a start condition and writes the device address, but this time the RW bit is a logic high to initiate the read access. Now, the master can read 1 to N bytes from the receiver. The receiver will first deliver the byte value at 0xFD, followed by the value at 0xFE. At this point the master knows the number of bytes waiting at the 0xFF register, and by acknowledging again, the data stream follows. The data transfer will stop once the master emits a not-acknowledge response or a stop condition is triggered after the last byte has been read.

Figure 7: I2C random read access
If "current address" is used, an address pointer in the receiver is used to determine which register to read. This address pointer will increment after each read operation unless it is already pointing at register $0 x F F$, the highest addressable register, in which case it remains unaltered.

The initial value of this address pointer at startup is $0 x F F$, so by default all current address read operations will repeatedly read register $0 x F F$ and receive the next byte of message data (or $0 x F F$ value if no message data is waiting).


Figure 8: I2C current address read access
Only after addressing the slave, the receiver starts the data stream. If the master does not read data from the receiver for a certain timeout, the receiver assumes that the communication is broken and stops the data stream, preventing an overflow of the output buffer. This timeout is 1.5 seconds by default. However, it can be extended by setting the CFG-I2C-EXTENDEDTIMEOUT configuration item to true (see the MAX-M10S interface description [3]). By disabling the timeout, the receiver will only interrupt the data stream when the buffer is full. The buffer can store up to 4 kB and the time for an overflow event depends on the number of messages enabled.

# 3.2.2.3 Write access 

The receiver does not provide any write access except for writing UBX and NMEA messages to the receiver, such as configuration or aiding data. Therefore, the register set mentioned in section I2C register layout is not writeable.Following the start condition from the master, the 7-bit device address and the RW bit (which is a logic low for write access) are clocked onto the bus by the master transmitter. The receiver answers with an acknowledge (logic low) response to indicate that it is responsible for the given address.

The master can write 2 to N bytes to the receiver, generating a stop condition after the last byte being written. To properly distinguish from the write access to set the address counter in random read accesses, the number of data bytes must be at least 2.


Figure 9: I2C write access

# 3.2.3 PIOs 

This section describes the PIOs supported by MAX-M10S. All PIO active voltage levels are related to the V_IO supply voltage. All the inputs have internal pull-up resistors in normal operation and can be left open if unused.
$\sim$ When assigning a different function to a PIO, ensure that the default function is disabled where applicable. For example, disable the I2C interface with the CFG-I2C-ENABLED configuration key if I2C pins are used for antenna supervisor functions.

### 3.2.3.1 RESET_N

MAX-M10S provides a RESET_N pin to reset the receiver. The RESET_N pin is input-only with an internal pull-up resistor to V_IO and should be left open for normal operation. Driving RESET_N low for at least 1 ms will trigger a reset of the receiver. The RESET_N complies with the V_IO level and can be actively driven high.
$\sim$ Use RESET_N only in critical situations to recover the receiver. RESET_N resets the receiver and clears the BBR content including receiver configuration, real-time clock (RTC), and GNSS orbit data, triggering a cold start.
$\sim$ No capacitor should be placed at RESET_N to GND, otherwise it could trigger a reset on every startup.

### 3.2.3.2 SAFEBOOT_N

The SAFEBOOT_N pin is for future service, updates and reconfiguration.
$\sim$ The SAFEBOOT_N pin is internally connected to the TIMEPULSE pin through a $1 \mathrm{k} \Omega$ series resistor.

### 3.2.3.3 TIMEPULSE

The MAX-M10S features one time pulse output at the TIMEPULSE pin. This can only be configured in PIO04. The details about this feature are explained in the section Time pulse.The TIMEPULSE and SAFEBOOT_N functions share the same internal IC function. If this pin is low at receiver startup, the receiver will enter safeboot mode. However, in normal operation the pin outputs the time pulse signal. Make sure there is no load on this pin that could pull it low at startup.

# 3.2.3.4 LNA_EN 

The system can turn an optional external LNA on and off using the LNA_EN signal to optimize the power consumption. The LNA is turned on when LNA_EN is "high".

The LNA_EN signal is also used internally in MAX-M10S to control the integrated LNA. The polarity cannot be changed.

The LNA_EN signal can also be used as a part of antenna supervisor circuit to control an external LNA or antenna power supply.

### 3.2.3.5 EXTINT

MAX-M10S supports external interrupts at the EXTINT pin. The EXTINT pin has a fixed input voltage threshold with respect to V_IO. It can be used for functions such as accurate external Frequency assistance, Time assistance and Time mark reporting.

The EXTINT pin enables External control for host-controlled on/off operation of the receiver, and as a wake-up source for power save mode on/off operation (PSMOO). If configured for host-controlled on/off operation, the internal pull-up is disabled. Make sure the EXTINT input is always driven within the defined voltage level by the host.

The EXTINT pin can also be configured for another functionality.
EXTINT functionality is only available at the EXTINT pin.

### 3.2.3.6 TX_READY

The receiver has an internal message buffer for storing bytes to be sent to the host application. TX-ready feature in TX_READY pin enables I2C to have an associated signal to indicate that the buffer has bytes to be transmitted. The host application can wait on the signal instead of polling the interface.

The TX-ready signal is enabled and assigned to a selected pin with CFG-TXREADY configuration items. The polarity of the signal (active-low or active-high) and the threshold for amount of bytes in the buffer must also be configured. When the number of bytes in the buffer reaches the threshold, the TX-ready signal becomes active. The signal stays active until all of the bytes in the buffer have been transferred. The receiver has additional small transmit buffer for each interface. Up to 16 bytes may still need to be transferred to the host after the TX-ready signal has become inactive.

The TX-ready signal can be assigned to any pin. Old function on the pin must be disabled before the assigment. Pin assignment can be verified with the UBX-MON-HW3 message.

The threshold value of the CFG-TXREADY-THRESHOLD is presented as 8-byte (64 bit) chunks. Divide the desired threshold value by 8. E.g., value of 128 sets the TX-ready signal activation threshold to 1024 bytes. The threshold should not be set above 2048 bytes (256 8-byte chunks). Otherwise, the TX-ready signal may not be activated in time, and some messages may get discarded.

### 3.2.3.6.1 Extended TX timeout

If the host does not communicate over I2C for more than 1.5 seconds, the receiver assumes that the host is no longer using this interface and no more packets are scheduled for this interface. This mechanism can be changed by enabling "extended TX timeouts" (configuration key CFG-I2C-EXTENDEDTIMEOUT). When enabled, the receiver delays idling the interface until the allocated and undelivered bytes for this interface reach 4 kB . This feature is especially useful when using the TXready feature with a message output rate of less than once per second, and fetching data only when available, determined by the TX_READY pin becoming active.

# 3.3 Antenna 

This section explains the antenna supervisor feature and the available implementation options.

### 3.3.1 Antenna supervisor

An active antenna supervisor provides the means to check the antenna for open and short circuits and to shut off the antenna supply if a short circuit is detected. Once enabled, the active antenna supervisor produces status messages that are reported in NMEA and/or UBX protocols. MAX-M10S supports two antenna supervisor variants: three-pin and two-pin implementations.

The three-pin antenna supervisor is able to detect short and open circuits and control the antenna supply. The two-pin antenna supervisor is a reduced version which is able to control the antenna supply and detect short circuits.

An overview of the two antenna supervisor variants is given in Table 15. It is recommended to make use of the full capabilities of the antenna supervisor (detect open and short circuits, and control the antenna supply).

The antenna supervisor can be configured through the CFG-HW-ANT_* configuration items. This includes enabling and disabling as well as changing the polarity of each signal. The current configuration of the active antenna supervisor can also be checked by polling the related CFGHW_ANT_* configuration items.

The active antenna status can be determined by polling the UBX-MON-RF message or checking the NMEA notice messages. If an antenna is connected, the initial state after power-up is "Active Antenna OK" in the UBX-MON-RF message.

| Features | Three-pin | Two-pin |
| :-- | :-- | :-- |
| Short detection | Yes | Yes |
| Open detection | Yes | No |
| External components | Discrete and IC | Discrete and IC |
| Number of PIOs needed | Three | Two |

Table 15: Antenna supervisor overview

### 3.3.1.1 Three-pin antenna supervisor

An active antenna supervisor circuit uses the ANT_DETECT, ANT_OFF_N, and ANT_SHORT_N signals. The ANT_OFF_N signal is already enabled and assigned to the LNA_EN pin in MAX-M10S. The ANT_DETECT and ANT_SHORT_N signals can be assigned to any unused PIOs, which may require disabling the previous function of the PIOs. For example, the open circuit detection uses the ANT_DETECT signal, "high" = Antenna detected (antenna consumes current); "low" = Antenna not detected (no current drawn). To enable the three-pin antenna supervisor, the ANT_DETECT and ANT_SHORT_N signals must be enabled in the receiver configuration. The polarity of the ANT_DETECT and ANT_SHORT_N signals must also be defined in the receiver configuration based on the design use case.

The antenna can be supplied by VCC_RF or an external supply. Note that the supply voltage must be clean, as any noise could directly couple into the RF part of the GNSS receiver which affecting the overall GNSS performance.Refer to Reference designs for antenna supervisor examples and the required configuration.
Figure 10 presents the required three-pin antenna supervisor circuit and subsequent sections describe how to enable and monitor each feature.


Figure 10: MAX-M10S three-pin antenna supervisor
Table 16 presents a list of the external components required for implementing the three-pin antenna supervisor design in Figure 10. Refer to External components for the recommended parts and specification.

| Part | Description |
| :-- | :-- |
| C14 | Filtering capacitor |
| L3 | DC infeed inductor |
| T1, T2 | p-channel, n-channel MOSFET acting as a switch to control the antenna supply |
| U6 | Comparator (op-amp) |
| U7, U8 | Open drain buffers to shift voltage levels |
| R7 | Passive pull-up to control T1 |
| R8 | Current limiter in the event of a short circuit |
| R5 | Defines the threshold of the comparator |
| R6 | Defines the threshold of the comparator |

Table 16: Components in antenna supervisorThe threshold voltage (V_REF) of the comparator is defined by R5 and R6. It can be calculated as: $V_{-} R E F=R 6 /(R 6+R 5)^{*} V_{-} A N T$.

The open drain buffers shown in Figure 10 are not needed if V_ANT is the same voltage level as V_IO.

# 3.3.1.2 Two-pin antenna supervisor 

The reduced functionality antenna supervisor circuit is connected to two signals: antenna control (ANT_OFF_N) and antenna status detection (ANT_SHORT_N). The ANT_OFF_N signal is already enabled and assigned to the LNA_EN pin in MAX-M10S and the ANT_SHORT_N signal can be assigned to any unused PIO, which may require disabling the previous function of the PIO. To enable the reduced antenna supervisor, the ANT_SHORT_N signal must be enabled in the receiver configuration. The polarity of the ANT_SHORT_N signal must also be defined in the receiver configuration based on the design use case.

The antenna can be supplied by VCC_RF or an external supply. Note that the supply voltage must be clean, as any noise could directly couple into the RF part of the GNSS receiver affecting the overall GNSS performance.

Refer to Reference designs for antenna supervisor examples and the required configuration.
Figure 11 presents the required two-pin antenna supervisor circuit and subsequent sections describe how to enable and monitor each feature.


Figure 11: MAX-M10S two-pin antenna supervisor
Table 17 presents a list of the external components required for implementing the two-pin antenna supervisor design in Figure 11. Refer to External components for the recommended parts and specification.

| Part | Description |
| :-- | :-- |
| C14 | Filtering capacitor || Part | Description |
| :-- | :-- |
| T1, T2 | p-channel, n-channel MOSFET acting as a switch to control the antenna supply |
| U7 | Open drain buffers to shift voltage levels |
| R7 | Passive pull-up to control T1 |
| R8 | Current limiter in the event of a short circuit |

Table 17: Components in two-pin antenna supervisor
The open drain buffer shown in Figure 11 is not needed if V_ANT is the same voltage level as V_IO.

# 3.3.1.3 Antenna voltage control - ANT_OFF_N 

The antenna voltage control is enabled by default in MAX-M10S with the configuration item CFGHW-ANT_CFG_VOLTCTRL set to true (1).

The antenna status (as reported in UBX-MON-RF and UBX-INF-NOTICE messages) is not reported unless the antenna voltage control has been enabled.

Result:

- UBX-MON-RF: Antenna status = OK. Antenna power status = ON.
- ANT_OFF_N = active low. The pin is pulled high to enable an external antenna or LNA.

Startup message at power-up if the configuration is stored:
\$GNTXT, 01, 01, 02,ANTSUPERV=AC *00
\$GNTXT, 01, 01, 02, ANTSTATUS=INIT*3B
\$GNTXT, 01, 01, 02, ANTSTATUS=OK*25
ANTSUPERV=AC indicates that antenna control is activated.

### 3.3.1.4 Antenna short detection - ANT_SHORT_N

Enable the antenna short detection by setting the configuration item CFG-HW-ANT_CFG_SHORTDET to true (1).

Result:

- UBX-MON-RF: Antenna status = OK. Antenna power status = ON.
- ANT_OFF_N = active low to disable an external antenna. Therefore, the pin is pulled high to enable an external antenna.
- ANT_SHORT_N = active low to report a short circuit. The pin is default high (PIO pull-up enabled).

Startup message at power-up if the configuration is stored:
\$GNTXT, 01, 01, 02,ANTSUPERV=AC SD *37
\$GNTXT, 01, 01, 02, ANTSTATUS=INIT*3B
\$GNTXT, 01, 01, 02, ANTSTATUS=OK*25
ANTSUPERV=AC SD indicates that antenna control and short detection are activated.
If a short circuit is detected in the antenna (ANT_SHORT_N pulled low):
\$GNTXT, 01, 01, 02, ANTSTATUS=SHORT*73

- UBX-MON-RF: Antenna status = SHORT. Antenna power status = ON (automatic power-down is not enabled, CFG-HW-ANT_CFG_PWRDOWN is off by default).- ANT_OFF_N = high (external antenna enabled).

If CFG-HW-ANT_CFG_PWRDOWN has been enabled previously (set to true), the polarity of the ANT_OFF_N signal changes to power down (disable) the antenna supply when a short is detected.

After a detected antenna short, the reported antenna status continues to be reported as a SHORT. If auto-recovery is enabled for the antenna short detection, the antenna status can recover after a timeout of 60 seconds. Recovering the antenna status immediately requires either a power cycle or switching the antenna short detection off and on again.

# 3.3.1.5 Antenna short detection auto-recovery 

Enable the antenna short detection auto-recovery by setting the configuration item CFG-HWANT_CFG_RECOVER to true (1).

To use the auto-recovery feature, enable CFG-HW-ANT_CFG_PWRDOWN which requires CFG-HW-ANT_CFG_SHORTDET and CFG-HW-ANT_CFG_VOLTCTRL to be enabled.

Result:

- UBX-MON-RF: Antenna status = OK. Antenna power status = ON.
- ANT_OFF_N = active low. The pin is pulled high to enable an external antenna.
- ANT_SHORT_N = active low. The pin is default high (PIO pull-up enabled, to be pulled low if a SHORT is detected).

Startup message at power-up if the configuration is stored:
\$GNTXT, 01, 01, 02,ANTSUPERV=AC SD PDoS SR*3E
\$GNTXT, 01, 01, 02, ANTSTATUS=INIT*3B
\$GNTXT, 01, 01, 02, ANTSTATUS=OK*25
ANTSUPERV=AC SD PDoS SR (indicates short circuit recovery added - SR)
If short circuit is detected (ANT_SHORT_N pulled low):
\$GNTXT, 01, 01, 02, ANTSTATUS=SHORT*73

- UBX-MON-RF: Antenna status = SHORT. Antenna power status = OFF (automatic power-down is enabled).
- ANT_OFF_N = low (external antenna disabled).

After a timeout period of 60 seconds, the receiver retests the short circuit condition by enabling the antenna (i.e. pulling ANT_OFF_N high).

If a short is not present, the receiver reports antenna condition is OK:
\$GNTXT, 01, 01, 02, ANTSTATUS=OK*25
UBX-MON-RF: Antenna status = OK. Antenna power status = ON.

### 3.3.1.6 Antenna open circuit detection - ANT_DETECT

Enable the antenna open circuit detection by setting the configuration item CFG-HWANT_CFG_OPENDET to true (1).

Result:

- UBX-MON-RF: Antenna status = OK. Antenna power status = ON.
- ANT_OFF_N = active low. The pin is pulled high to enable an external antenna.- ANT_SHORT_N = active low. The pin is default high (PIO pull-up enabled, to be pulled low if a SHORT is detected).
- ANT_DETECT = active high. The pin is default high (PIO pull-up enabled, to be pulled low if the antenna is not detected).

Startup message at power-up if the configuration is stored:

```
$GNTXT,01,01,02,ANTSUPERV=AC SD OD PDoS SR*15
$GNTXT,01,01,02,ANTSTATUS=INIT*3B
$GNTXT,01,01,02,ANTSTATUS=OK*25
ANTSUPERV=AC SD OD PDoS SR (indicates open circuit detection added - OD)
```

If ANT_DETECT is pulled low to indicate no antenna connected:

```
$GNTXT,01,01,02,ANTSTATUS=OPEN*35
```

If ANT_DETECT is left floating or pulled high to indicate antenna connected:

```
$GNTXT,01,01,02,ANTSTATUS=OK*25
```

# 3.3.1.7 Antenna status reporting 

The antenna detection and antenna power status that is available in UBX-MON-RF and NMEA notice messages, is based on the antenna's physical state. The required antenna supervisor configuration keys depend on the selected antenna supervisor implementation (three-pin or two-pin).

Table 18 and Table 19 present a summary of the antenna status that is available in the antStatus and antPower fields of the UBX-MON-RF message. Refer to the interface description [3] for more information.

| Status | Description |
| :-- | :-- |
| DON'T KNOW | Antenna status is unknown. |
| INIT | Antenna power control feature is initialized (if CFG-HW-ANT_VOLTCTRL is enabled). |
| SHORT | A short is detected from the antenna input. That is, a lot of current is drawn from the active antenna. |
| OPEN | Antenna is not detected. That is, little or no current is drawn from the active antenna. |
| OK | Antenna is detected and no short is detected. |

Table 18: Available antenna detection status

| Status | Description |
| :-- | :-- |
| DON'T KNOW | CFG-HW-ANT_VOLTCTRL not configured. |
| OFF | GNSS OFF or a short is detected and CFG-HW-ANT_PWRDOWN is enabled. Note that this status <br> also applies when GNSS is restarted via CFG-RST or implicitly via CFG-GNSS, when GNSS selection is <br> reconfigured, or when GNSS is stopped in software standby mode and the off state of the power save <br> mode on/off (PSMOO). |
| ON | GNSS ON and no short/open is detected from the antenna input. Similarly, when there is a short and <br> CFG-HW-ANT_PWRDOWN is not enabled or auto-recovery is enabled. |

Table 19: Available antenna power status
Table 20 shows some possible combinations of the antenna supervisor configuration and the expected antenna status based on the physical state of the antenna. Note that the short detection takes priority over the open detection and " $X$ " in Table 20 implies an unconfigured or undetected physical state. In addition, CFG-HW-ANT_PWRDOWN requires that CFG-HW-ANT_CFG_VOLTCTRL and CFG-HW-ANT_CFG_SHORTDET are enabled. Likewise, CFG-HW-ANT_RECOVER requires CFG-HW-ANT_PWRDOWN to be enabled.The antenna supervisor is re-initialized after issuing a reset with RESET_N pin or changing any of the antenna supervisor configuration keys. Therefore, if the default configuration has changed, it is recommended to save the antenna supervisor configuration to BBR to ensure that the updated configuration is applied after a reset.

|  Configuration keys |  |  |  |  | Physical antenna state |  | Reported antenna status | |
| --- | --- | --- | --- | --- | --- | --- | --- | --- |
|  VOLTCTRL | SHORTDET | OPENDE | PWRDOWN | RECOVER | Short circuit Open circuit |  | antPower | antStatus  |
|  TRUE | $X$ | $X$ | $X$ | $X$ | NO | NO | ON | OK  |
|  TRUE | FALSE | $X$ | $X$ | $X$ | $X$ | NO |  | |
|  TRUE | $X$ | FALSE | $X$ | $X$ | NO | $X$ |  | |
|  TRUE | FALSE | FALSE | $X$ | $X$ | $X$ | $X$ |  | |
|  TRUE | FALSE | TRUE | $X$ | $X$ | $X$ | YES | ON | OPEN  |
|  TRUE | $X$ | TRUE | $X$ | $X$ | NO | YES |  | |
|  TRUE | TRUE | $X$ | FALSE | $X$ | YES | $X$ | ON | SHORT  |
|  TRUE | TRUE | $X$ | TRUE | $X$ | YES | $X$ | OFF | SHORT  |
|  FALSE | TRUE | $X$ | $X$ | $X$ | YES | $X$ | UNKNOWN | SHORT  |
|  FALSE | FALSE | TRUE | $X$ | $X$ | $X$ | YES | UNKNOWN | OPEN  |
|  FALSE | $X$ | TRUE | $X$ | $X$ | NO | YES | UNKNOWN | OPEN  |

Table 20: Antenna supervisor configuration and antenna states

# 3.4 Forcing receiver reset

GNSS receivers typically make a distinction between cold, warm, and hot start based on the type of valid information the receiver has during the restart.

- Cold start: in the cold start mode, the receiver has no information from the last position (e.g. time, velocity, frequency etc.) at startup. Therefore, the receiver must search the full time and frequency space, and all possible satellite numbers. If a satellite signal is found, it is tracked to decode the ephemeris (18-36 seconds under strong signal conditions), while the other channels continue to search satellites. Once there is a sufficient number of satellites with valid ephemeris, the receiver can calculate position and velocity data. Other GNSS receiver manufacturers call this the Factory startup mode.
- Warm start: in the warm start mode, the receiver has approximate information for time, position, and coarse satellite position data (Almanac). In this mode, the receiver normally needs to download ephemeris after power-up before it can calculate position and velocity data. As the ephemeris data is usually outdated after 4 hours, the receiver typically starts with a warm start if it has been powered down for more than 4 hours. In this scenario, several augmentations are possible. See Multiple GNSS assistance.
- Hot start: in the hot start mode, the receiver has been powered down only for a short time (4 hours or less), so that its ephemeris is still valid. Since the receiver does not need to download ephemeris again, this is the fastest startup method.

Using the UBX-CFG-RST message, you can force the receiver to reset and clear data, in order to see the effects of maintaining/losing such data between restarts. For this purpose, use the navBbrMask field in the UBX-CFG-RST message to initiate hot, warm, and cold starts, or a combination of startup modes.

The reset type can also be specified. This is not related to GNSS, but to the way the software restarts the system.

- Hardware reset uses the on-chip watchdog to electrically reset the chip. This is an immediate asynchronous reset. No stop events are generated.- Controlled software reset terminates all running processes in an orderly manner. Once the system is idle, restarts the receiver operation, reloads its configuration and starts to acquire and track GNSS satellites.
- Controlled software reset (GNSS only) only restarts the GNSS tasks, without reinitializing the full system or reloading any stored configuration.
- Hardware reset (after shutdown) uses the on-chip watchdog to reset the receiver after shutdown.
- Controlled GNSS stop stops all GNSS tasks. The receiver is not restarted, but stops any GNSSrelated processing.
- Controlled GNSS start starts all GNSS tasks.

Table 21 below contains an overview of the different reset types and the data that is cleared.

|  Reset type | Clears RAM | Clears BBR  |
| --- | --- | --- |
|  0x00 - Hardware reset (immediately), | Yes | Yes  |
|  0x04 - Hardware reset (after shutdown) |  | |
|  0x01 - Controlled Software reset | Yes | No  |
|  0x02 - Controlled Software reset (GNSS only), | No | No  |
|  0x08 - Controlled GNSS stop, |  | |
|  0x09 - Controlled GNSS start |  | |
|  RESET_N pin | Yes | Yes  |

Table 21: Overview of the available reset types

# 3.5 Security

The security concept of MAX-M10S covers:

- the integrity of the receiver
- communication between the receiver and the GNSS satellites

Some security functions monitor and detect threats and report them to the host system. Other functions mitigate threats and allow the receiver to operate normally.

### 3.5.1 Configuration locking

The receiver configuration can be locked so that further changes are no longer possible. The configuration can be locked by setting the configuration item CFG-SEC-CFG_LOCK to "true". This item can be set in the same way as all other configuration items on various layers.

If the configuration lock is set in BBR, it remains locked until the BBR is cleared. To test the function, set it in the RAM configuration layer. After the receiver's power cycle, the information in this layer is lost and the configuration lock is not set anymore.

### 3.6 Power management

u-blox receivers support different operating modes. These modes represent strategies of controlling the acquisition and tracking engines to achieve either the best possible performance or good performance with reduced power consumption.

### 3.6.1 Continuous mode

MAX-M10S uses dedicated signal processing engines optimized for signal acquisition and tracking. The acquisition engine actively searches for and acquires signals during cold starts or when insufficient signals are available during navigation. The tracking engine continuously tracks anddownloads all the almanac data and acquires new signals as they become available during navigation. The tracking engine consumes less power than the acquisition engine.

The current consumption is lower when a valid position is obtained quickly after the start of the receiver navigation, the entire almanac has been downloaded, and the ephemeris for each satellite in view is valid. If these conditions are not met, the search for the available satellites takes more time and consumes more power.

# 3.6.2 Power save mode 

Power save mode (PSM) allows a reduction in system power consumption by selectively switching parts of the receiver on and off. It is enabled with CFG-PM-OPERATEMODE and configured with items in the CFG-PM group.

Power save mode (PSM) has two modes of operation:

- Power save mode cyclic tracking (PSMCT) operation is used when position fixes are required in short periods of 0.5 s to 10 s .
- Power save mode on/off (PSMOO) operation is used for periods longer than 10 s , and can be in the order of minutes, hours, or days.

The mode of operation can be configured, and depending on the setting, the receiver demonstrates different behavior. In on/off operation the receiver switches between phases of startup/navigation and phases with low or almost no system activity (backup/sleep). In cyclic tracking the receiver does not shut down completely between fixes, but uses low-power tracking instead.

In PSMOO mode, the RAM memory is cleared during the off periods. Consequently, store the configuration in the BBR memory to maintain the settings.

GPS, GLONASS, BeiDou B1I, Galileo and QZSS signals are supported in power save mode. BeiDou B1C signal is not supported. The receiver is unable to download or process any SBAS data in power save mode and it is therefore recommended to disable SBAS.

BeiDou B1C is not supported in power save mode.

### 3.6.2.1 Operation

PSM is based on a state machine with five different states: Inactive for update, Inactive for search, Acquisition, Tracking and Power optimized tracking (POT) state.

- Inactive states: most parts of the receiver are switched off.
- Acquisition state: the receiver actively searches for and acquires signals. Maximum power consumption.
- Tracking state: the receiver continuously tracks and downloads data. Less power consumption than in the acquisition state.
- POT state: the receiver repeatedly loops through a sequence of tracking (Track), calculating the position fix (Fix), and entering an idle period (Idle). No new signal is acquired and no data is downloaded. The power consumption is much lower than in the tracking state.

The PSM state machine is described in Figure 12.

Figure 12: State machine

# 3.6.2.2 Acquisition timeout 

The receiver has internal, external, and user-configurable mechanisms that determine the time to be spent in acquisition state. This logic is put in place to ensure good performance and low power consumption in different environments and scenarios. This collective logic is referred to as acquisition timeout.

The configuration items related to acquisition timeout are described in section Configuration.
Internal mechanisms:

- If the receiver is able to acquire weak signals but not of the quality needed to get a fix, it will transition to the "Inactive for search" state after the timeout configured in MAXACQTIME or earlier if too few signals are acquired.
- If the receiver is unable to acquire any signals or it acquires a small number of extremely bad signals (e.g., no sky view), it will transition to the "Inactive for search" state after the timeout configured in MAXACQTIME.

User-configurable mechanisms:

- MINACQTIME is the minimum time that the receiver will spend in the "Acquisition" state. MINACQTIME is applicable only when no or very poor GNSS signal is available.
- MAXACQTIME is the maximum time that the receiver will spend in the "Acquisition" state.
- DONOTENTEROFF forces the receiver to stay awake and in the "Acquisition" state even when a fix is not possible.

External mechanisms:

- The receiver is forced to stay awake if EXTINTWAKE is enabled and the EXTINT pin is set to "high". The receiver is forced to stay in the "Inactive for search/Fix" states if EXTINTBACKUP is enabled and the EXTINT pin is set to "low".
- The receiver is forced to stay awake if EXTINTINACTIVE is enabled and the EXTINT pin is toggled. If EXTINT pin state is not changed for a longer time than EXTINTINACTIVITY, the receiver enters the "Inactive for search/Fix" states.# 3.6.2.3 Cyclic tracking 

Power save mode cyclic tracking (PSMCT) operation is described in Figure 13.
PSMCT supports 1 Hz and 2 Hz navigation update rates. In addition, longer update periods from 2 s to 10 s are supported at 1 s steps.


Figure 13: Cyclic tracking operation

- When the receiver is switched on, it first enters the "Acquisition" state. A larger number of signals tracked later helps the receiver to remain in the "POT" state if some signals get blocked and are lost. This may reduce the overall power consumption.
- If the receiver is able to acquire a valid position fix (one passing the navigation output filters) within the time given by the Acquisition timeout, it switches to the "Tracking" state and the ONTIME starts. Otherwise it enters the "Inactive for search" state and restarts after the configured search period (minus a start-up margin).
- Once the ONTIME is over, the "POT" state is entered. Setting the ONTIME to zero causes the receiver to enter the "POT" state as soon as possible.
- In the "POT" state the receiver continues to output position fixes according to the CFG-RATE-*.
- If the signal becomes weak or is lost during the "POT" state, the "Tracking" state is entered.
- Once the signal is good again and the newly started ONTIME is over, the receiver will re-enter the "POT" state.
- If the receiver cannot get a position fix in the "Tracking" state, it enters the "Acquisition" state. Should the acquisition fail as well, the "Inactive for search" state is entered. If DONOTENTEROFF is enabled and no fix is possible, the receiver will remain in the "Acquisition" state until a fix is possible and it will never enter the "Inactive for search" state.

### 3.6.2.4 On/Off mode

Power save mode on-off (PSMOO) operation is described in Figure 14.
PSMOO requires an RTC to maintain time.


Figure 14: On/off mode operation

- When the receiver is switched on, it first enters the "Acquisition" state.
- If it is able to acquire a valid position fix (one passing the navigation output filters) within the time given by the Acquisition timeout, it switches to the "Tracking" state and the ONTIMEstarts. Otherwise it enters the "Inactive for search" state and restarts after the configured search period (minus a startup margin).

- Once the ONTIME is over, the "Inactive for update" state is entered and the receiver restarts according to the configured update grid defined by GRIDOFFSET.
- If the signal is lost while in the "Tracking" state, the "Acquisition" state is entered. If the signal is not found within the acquisition timeout, the receiver enters the "Inactive for search" state. Otherwise the receiver will re-enter the "Tracking" state and stay there until the newly started ONTIME is over.

Entering the off state of the PSMOO operation clears the RAM memory including the receiver configuration. To maintain the configuration in PSMOO operation, store it on both RAM and battery-backed RAM (BBR) layers. Configuration in an optional flash memory is always maintained.

# 3.6.2.5 External control 

The operation of power save mode can be controlled externally using the EXTINT pin. This external control allows the user to decide when to wake up the receiver to obtain a fix and when to force the receiver into backup mode to save power. Operating the receiver externally through the EXTINT pin will override internal functions that coincide with that specific operation.

Enabling EXTINTWAKE prevents the receiver from entering Inactive states for as long as the EXTINT pin is held "high". In PSMOO, the receiver will therefore always be in the "Acquisition" or the "Tracking" state. In PSMCT, the receiver can in addition be in the "POT" state. When EXTINT is set "low" the receiver will continue with its configured behavior.

Enabling EXTINTBACKUP forces the receiver to enter Inactive states for as long as the EXTINT pin is held "low" until the next wakeup event. Any wakeup event can wake up the receiver even if the EXTINT pin is held "low". In this case, the receiver only wakes up to read the configuration pins and then re-enters the Inactive state.

If both EXTINTWAKE and EXTINTBACKUP are enabled at the same time, the receiver PSM operation is completely under external control. Setting EXTINT "high" wakes up the receiver to get a position fix and setting "low" puts the receiver into backup mode.

EXTINT pin control can also be used in continuous mode.
In PSMOO, an external wakeup source can be set. Any wake-up event will restart the receiver to try to obtain a position fix. Wakeup signals have no effect if the receiver is already in the "Acquisition", "Tracking", or "POT" state.

Setting the update period POSUPDATEPERIOD to zero causes the receiver to wait in the "Inactive for update" state until the host wakes it up. Setting the search period ACQPERIOD to zero causes the receiver to wait in the "Inactive for search" state indefinitely after an unsuccessful startup.

External wake-up source is required when setting update or search period to zero.
The wake-up sources are:

- Rising or falling edge on the UART RX pin
- Rising or falling edge on the EXTINT pin
- Rising or falling edge on the SPI CS pin
- Rising edge on RESET_N pin

Backup modes can also be used to control the receiver state externally.# 3.6.2.6 Configuration

Power save mode (PSM) is enabled and disabled with CFG-PM-OPERATEMODE and configured with items in the CFG-PM group listed in Table 22.

When using power save mode on/off (PSMOO) operation, set the OPERATEMODE as the last PSM configuration key to prevent the receiver entering the off state before all intended PSM configuration keys are set.

|  Config key | Description  |
| --- | --- |
|  OPERATEMODE | Receiver mode of operation  |
|  POSUPDATEPERIOD | Time between two position fix attempts in on/off power save mode  |
|  ACQPERIOD | Time between two acquisition attempts if the receiver is unable to get a position fix  |
|  GRIDOFFSET | Time offset of update grid with respect to start of week  |
|  ONTIME | Time the receiver remains in the "Tracking" state and produces position fixes  |
|  MINACQTIME | Minimum time the receiver spends in the "Acquisition" state  |
|  MAXACQTIME | Maximum time in the "Acquisition" state  |
|  DONOTENTEROFF | Receiver does not enter the "Inactive for search" state if it cannot get a position fix but
keeps indefinitely attempting a position fix instead  |
|  WAITTIMEFIX | Wait for time fix before entering the "Tracking" state  |
|  UPDATEEPH | Enables periodic ephemeris update  |
|  EXTINTWAKE | Enables EXTINT pin control to force receiver on  |
|  EXTINTBACKUP | Enables EXTINT pin control to force receiver in backup  |
|  EXTINTINACTIVE | Enter a backup state if EXTINT pin is inactive longer time than specified by
EXTINTINACTIVITY  |
|  EXTINTINACTIVITY | Specifies the inactivity period  |

Table 22: Power save mode configuration options in the CFG-PM group OPERATEMODE The mode of operation to use mainly depends on the update period: For short update periods (in the range of a few seconds), cyclic tracking should be configured. For long update periods (in the range of minutes or longer), only use on/off operation. See section On/Off mode and Cyclic tracking for more information on the two modes of operation.

POSUPDATEPERIOD, ACQPERIOD The update period POSUPDATEPERIOD specifies the time between successive position fixes. If no position fix can be obtained within the acquisition timeout, the receiver will retry after the time specified by the search period ACQPERIOD. Update and search periods are fixed with respect to an absolute time grid based on reference time standard (i.e., GPS time or UTC). They do not refer to the time of the last valid position fix or last position fix attempt. Where multiple GNSS can operate simultaneously, UTC time is used as the reference time standard.

The update period setting is ignored if the receiver is set into cyclic tracking mode. It only has an impact if the receiver is set to on/off mode. New settings are ignored if the update period or the search period exceeds the maximum number of milliseconds in a week. In that case the previously stored values remain effective.

GRIDOFFSET Once the receiver has a valid time, the update grid is aligned to the start of the week of the reference time standard (midnight between Saturday and Sunday). Before having a valid time, the update grid is unaligned. A grid offset shifts the update grid with respect to the start of the week of the reference time standard. The grid offset is not used in cyclic tracking operation.

ONTIME This specifies how long the receiver stays in the "Tracking" state before switching to the "POT" state in PSMCT or the "Inactive for update" state in PSMOO.MINACQTIME The receiver tries to obtain a position fix for at least the time given by MINACQTIME. If the receiver determines that it needs more time for the given starting conditions then it will automatically prolong this time. If MINACQTIME is set to zero, the receiver determines the time. Once the MINACQTIME has expired, the receiver will terminate the acquisition state if either a fix is achieved or if the receiver estimates that any signals received are insufficient (too weak or too few) for a fix to be possible.

MINACQTIME is applicable only when no or very poor GNSS signal is available.
MAXACQTIME This defines the maximum time that the receiver will spend in the "Acquisition" state. If the receiver is unable to acquire a valid position fix within this maximum time, it will transition to the "Inactive for search" state (if DONOTENTEROFF is disabled). Subsequently, the receiver will attempt to acquire another position fix according to the search period ACQPERIOD. If MAXACQTIME is set to zero, the receiver will autonomously determine the maximum time to spend in the "Acquisition" state. Note that shorter settings (below about 45 s ) will degrade an unaided receiver's ability to collect new Ephemeris data at low signal levels.

DONOTENTEROFF If this option is enabled, then when the receiver cannot get a fix it keeps attempting to acquire a position fix instead of entering the "Inactive for search" state. In other words, the receiver will never be in the "Inactive for search" state and therefore the search period ACQPERIOD and the minimum acquisition time MINACQTIME will be ignored.

WAITTIMEFIX A time fix is a fix type in which the receiver will ensure that the time is accurate and confirmed to within the limits set in CFG-NAVSPG. Enabling the WAITTIMEFIX option will force the receiver to stay in the "Acquisition" state until the time is known to be within the configured limits, then it will transition to the "Tracking" state. Take into account that enabling WAITTIMEFIX will delay the transition from the "Acquisition" state to the "Tracking" state by at least two extra seconds.

The quality of the position fixes can also be configured by setting the limits in the CFG-NAVSPG group. Setting harder limits in CFG-NAVSPG will typically prolong the time in the "Acquisition" state. When externally controlled, it is therefore necessary to ensure sufficient time for the receiver at startup. Refer to Acquisition timeout for more information. When internally controlled, the receiver can make good judgment on the time needed in the "Acquisition" state and no further adjustments will be needed.

UPDATEEPH To maintain the ability of a fast startup, the receiver needs to update its ephemeris data on a regular basis. This can be ensured by activating the update Ephemeris option UPDATEEPH. The ephemeris data is updated approximately every 30 minutes. Refer to Satellite data download for more information.

# 3.6.2.7 Satellite data download 

The receiver is not able to download satellite data (e.g. the ephemeris) while it is working in on/off or cyclic tracking operation. Therefore it has to temporarily switch to continuous operation for the time the satellites transmit the desired data. To save power the receiver schedules the downloads according to an internal timetable and only switches to continuous operation when data of interest is being transmitted by the satellites.

Each satellite transmits its own ephemeris data. Ephemeris data download is feasible when the corresponding satellite has been tracked with a sufficient C/NO over a certain period of time. The download is scheduled in a 30-minute grid or immediately when fewer than a certain number of visible satellites have valid ephemeris data.Almanac, ionosphere, UTC correction, and satellite health data are transmitted by all satellites simultaneously. Therefore these parameters can be downloaded when a single satellite is tracked with a sufficiently high C/N0.

Allowing more ephemerides to be downloaded before going into the "POT" or the "Inactive for update" state can help improve the quality of the fixes and reduce the number of wake ups needed to download ephemerides at the cost of extra time in the "Acquisition" state (only when an inadequate number of ephemerides are downloaded from tracked satellites).

# 3.6.3 Backup modes 

A backup mode is an inactive state where the power consumption is reduced to a fraction of that in operating modes. The receiver maintains time information and navigation data to speed up the receiver restart after backup or standby mode.

The MAX-M10S supports two backup modes: hardware backup mode and software standby mode.

### 3.6.3.1 Hardware backup mode

The hardware backup mode allows entering a backup state and resuming operation by switching the main power supplies on and off while maintaining a V_BCKP supply via, e.g. a battery. The receiver enters hardware backup mode if the VCC and V_IO supplies are removed.

V_BCKP must be supplied to maintain the backup domain (BBR and RTC) to allow better TTFF, accuracy, availability and power consumption at the next startup compared with a cold start. As V_IO is not supplied, the PIOs cannot be driven by an external host processor. If driving of the PIOs cannot be avoided, buffers are required for isolating the PIOs.

### 3.6.3.2 Software standby mode

Software standby mode is entered using the UBX-RXM-PMREQ message. V_IO and VCC must be supplied, however VCC supply is internally disabled to save power. The V_IO supply maintains the battery-backed RAM (BBR), RTC, and PIOs.

Entering the software standby mode clears the RAM memory including the receiver configuration. To maintain the configuration, store it on both RAM and layers.

The software standby mode can be set for a specific duration, or until the receiver is woken up by a signal at a wake-up source defined in UBX-RXM-PMREQ. The possible wake-up sources are UART RX, EXTINT, and/or SPI CS pin. Refer to the interface description [3] for more information on the UBX-RXM-PMREQ message. A system reset with the RESET_N signal also terminates the software standby mode, clears the BBR content and restarts the receiver.

As V_IO is supplied, the PIOs can be driven by an external host processor. No buffers are required for isolating the PIOs, which reduces cost.

The "force" flag must be set in UBX-RXM-PMREQ to enter software standby mode.
V_BCKP should be left open if not used.# 3.7 Time 

Maintaining receiver local time and keeping it synchronized with GNSS time is essential for proper timing and positioning functionality. This section explains how the receiver maintains local time and introduces the supported GNSS time bases.
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
