zfeuers1/z-zener-zero/components/MSD-12-A/MSD-12-A.md

**CUI Devices is now Same Sky! Learn More**

Additional Resources: Product Page | 3D Model | PCB Footprint **date** 11/01/2024 **page** 1 of 5

**MODEL: MSD-12-A | DESCRIPTION: MICRO SD CARD CONNECTOR**

**FEATURES**

- Micro SD card connector
- push in, auto eject out
- card detect switch
- gold flash
- surface mount
- UL94V-0



**SPECIFICATIONS**

|  parameter | conditions/description | min | typ | max | units  |
| --- | --- | --- | --- | --- | --- |
|  rated voltage |  |  |  | 30 | V  |
|  rated current |  |  |  | 0.5 | A  |
|  contact resistance¹ |  |  |  | 100 | mΩ  |
|  insulation resistance | at 500 Vdc, between adjacent circuits | 1,000 |  |  | MΩ  |
|  voltage withstand | for 1 minute, between adjacent circuits |  | 500 |  | Vdc  |
|  insertion force | at a rate of 25 mm/min |  |  | 10 | N  |
|  withdrawal force | at a rate of 25 mm/min | 0.5 |  |  | N  |
|  life |  |  | 5,000 |  | cycles  |
|  operating temperature |  | -45 |  | 75 | °C  |
|  flammability rating | UL94V-0 |  |  |  | |
|  RoHS | yes |  |  |  | |

Note: 1. When measured at 20 mV / 100 mA.

**SOLDERABILITY**

|  parameter | conditions/description | min | typ | max | units  |
| --- | --- | --- | --- | --- | --- |
|  reel storage | at relative humidity 40-70% | 16 | 22 | 28 | °C  |
| | reel opened: use within 1 month |  |  |  | |
| | reel unopened: up to 15 month shelf life |  |  |  | |
|  reflow soldering | see reflow profile |  |  | 250 | °C  |
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
